MadsRudolph/OvnProjekt/Oscilator/Digital_Oscillator/Digital_Oscillator_TestKit/Driverkredsløb/Driverkredsløb pcb skabelon v.1.pdf

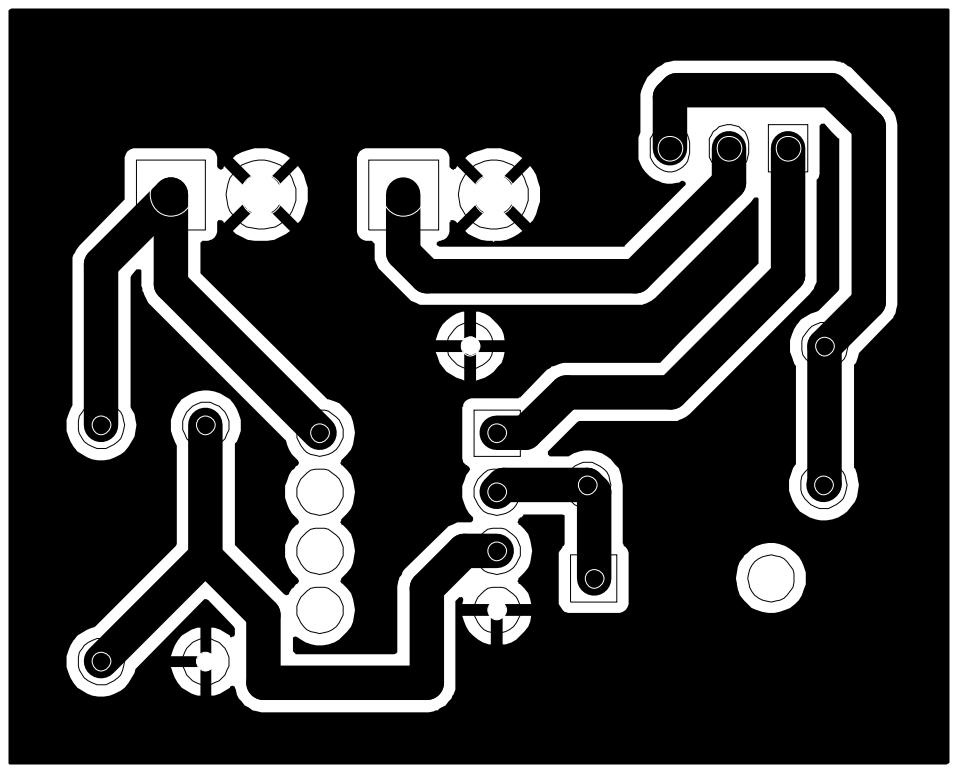
[picture p22: page 1]
