MadsRudolph/OvnProjekt/Afvigelsesdisplay/afvigelsesdisplay leds/leds/leds.kicad_pcb

## KiCad design Afvigelsesdisplay/afvigelsesdisplay leds/leds/leds.kicad_pcb (2025-09-05)

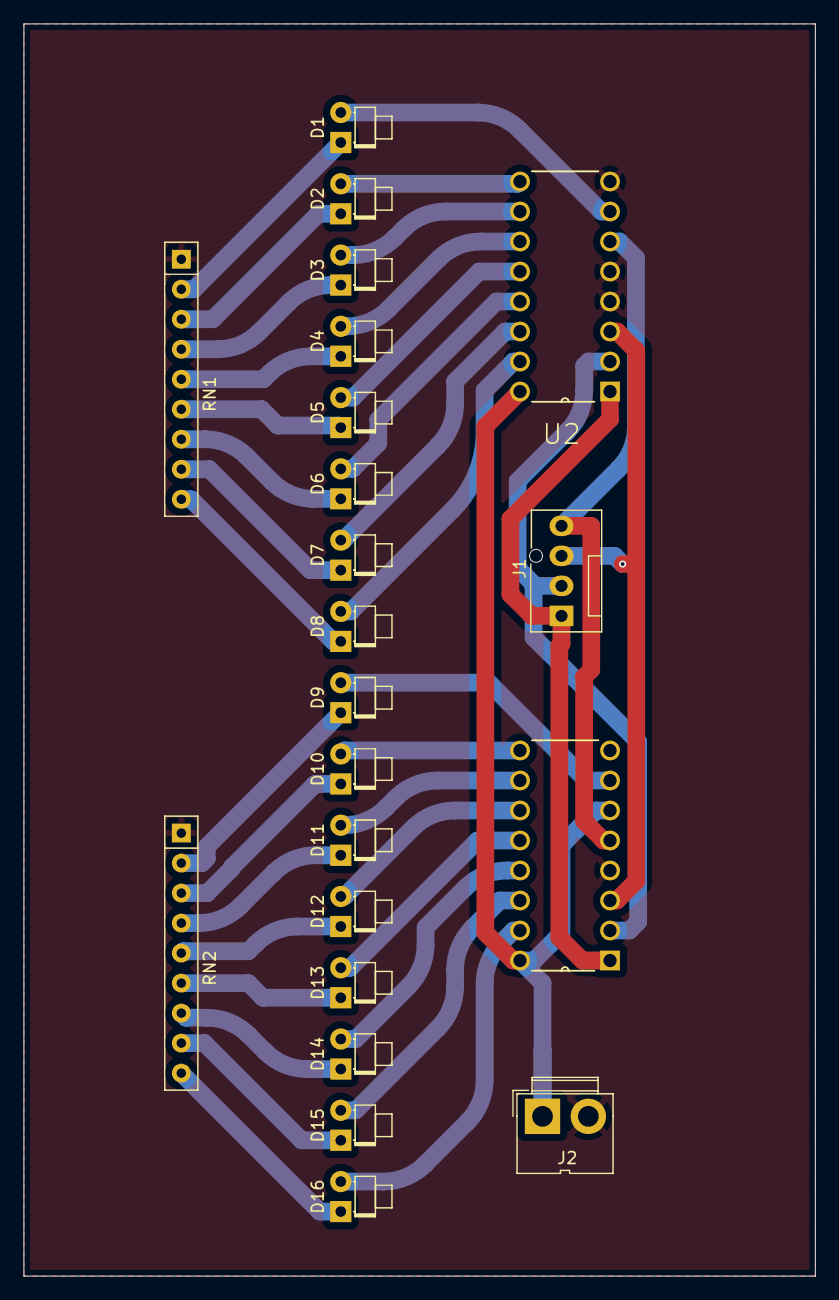
[picture p47: board leds.kicad_pcb from above]

Board: 2 copper layers, 67.0 x 106.0 mm, 22 parts (0 on the bottom side), 38 nets.

Parts:
D1, D2, D3, D4, D5, D6, D7, D8, D9, D10, D11, D12, D13, D14, D15, D16: LED; LED_D1.8mm_W1.8mm_H2.4mm_Horizontal_O1.27mm_Z8.2mm
J1: Conn_01x04_Socket; FanPinHeader_1x04_P2.54mm_Vertical
J2: Conn_01x02_Pin; JWT_A3963_1x02_P3.96mm_Vertical
RN1, RN2: R_Network08; R_Array_SIP9
U2, U3: 74HC238N; DIP254P762X420-16

Connections:
GND: J2.2, RN1.1 (common), RN2.1 (common), U2.4 (~E1), U2.5 (~E2), U2.8 (GND), U3.4 (~E1), U3.8 (GND)
unnamed: D1.2 (A), U2.7 (Y7)
unnamed: D1.1 (K), RN1.2 (R1)
unnamed: D2.2 (A), U2.9 (Y6)
unnamed: D2.1 (K), RN1.3 (R2)
unnamed: D3.2 (A), U2.10 (Y5)
unnamed: D3.1 (K), RN1.4 (R3)
unnamed: D4.2 (A), U2.11 (Y4)
unnamed: D4.1 (K), RN1.5 (R4)
unnamed: D5.2 (A), U2.12 (Y3)
unnamed: D5.1 (K), RN1.6 (R5)
unnamed: D6.2 (A), U2.13 (Y2)
unnamed: D6.1 (K), RN1.7 (R6)
unnamed: D7.2 (A), U2.14 (Y1)
unnamed: D7.1 (K), RN1.8 (R7)
unnamed: D8.2 (A), U2.15 (Y0)
unnamed: D8.1 (K), RN1.9 (R8)
unnamed: D9.2 (A), U3.7 (Y7)
unnamed: D9.1 (K), RN2.2 (R1)
unnamed: D10.2 (A), U3.9 (Y6)
unnamed: D10.1 (K), RN2.3 (R2)
unnamed: D11.2 (A), U3.10 (Y5)
unnamed: D11.1 (K), RN2.4 (R3)
unnamed: D12.2 (A), U3.11 (Y4)
unnamed: D12.1 (K), RN2.5 (R4)
unnamed: D13.2 (A), U3.12 (Y3)
unnamed: D13.1 (K), RN2.6 (R5)
unnamed: D14.2 (A), U3.13 (Y2)
unnamed: D14.1 (K), RN2.7 (R6)
unnamed: D15.2 (A), U3.14 (Y1)
unnamed: D15.1 (K), RN2.8 (R7)
unnamed: D16.2 (A), U3.15 (Y0)
unnamed: D16.1 (K), RN2.9 (R8)
unnamed: J1.1, U2.1 (A0), U3.1 (A0)
unnamed: J1.2, U2.2 (A1), U3.2 (A1)
unnamed: J1.3, U2.3 (A2), U3.3 (A2)
unnamed: J1.4, U2.6 (E3), U3.5 (~E2)
VCC: J2.1, U2.16 (VCC), U3.6 (E3), U3.16 (VCC)
